maxotar/metro/electrical/datasheets/ATtiny1616 20 Pin VQFN.PNG

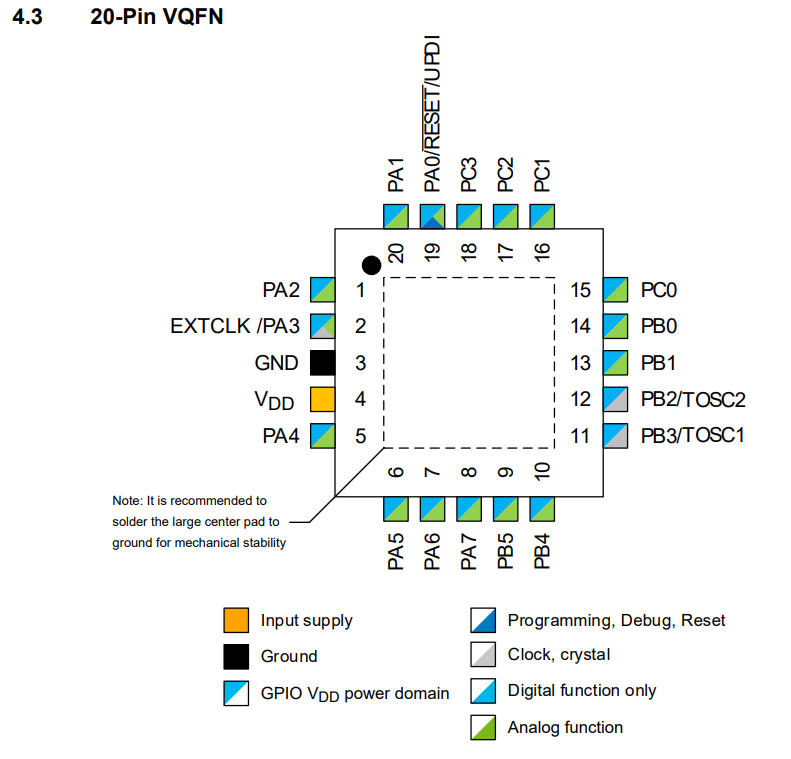
electrical/datasheets/ATtiny1616 20 Pin VQFN.PNG
