maxotar/metro/electrical/datasheets/ATtiny1616 MUX and PORTS.PNG

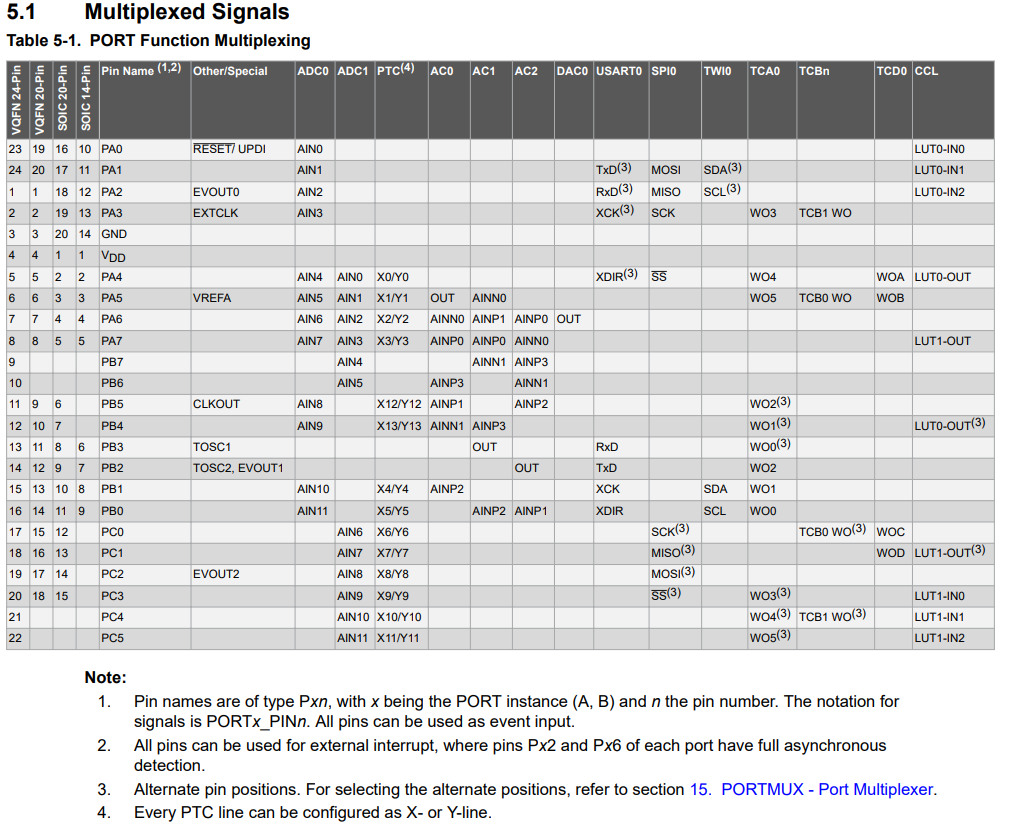
electrical/datasheets/ATtiny1616 MUX and PORTS.PNG
