maxotar/metro/electrical/references/Suggested Circuit DRV2605L.PNG

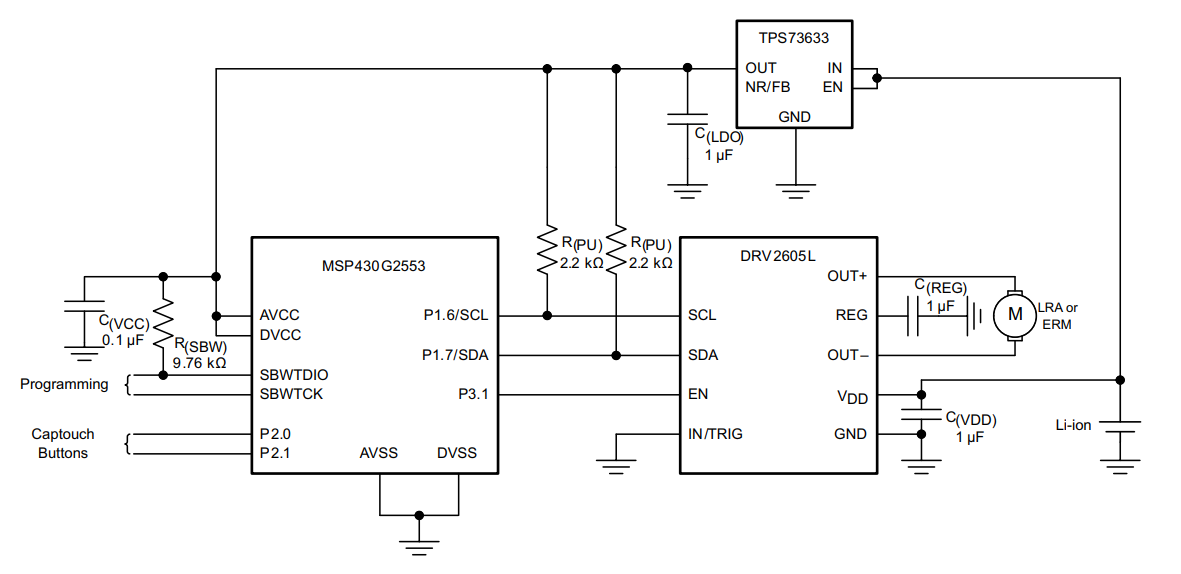
electrical/references/Suggested Circuit DRV2605L.PNG
