maxotar/metro/electrical/references/Suggested Layout DRV2605L.PNG

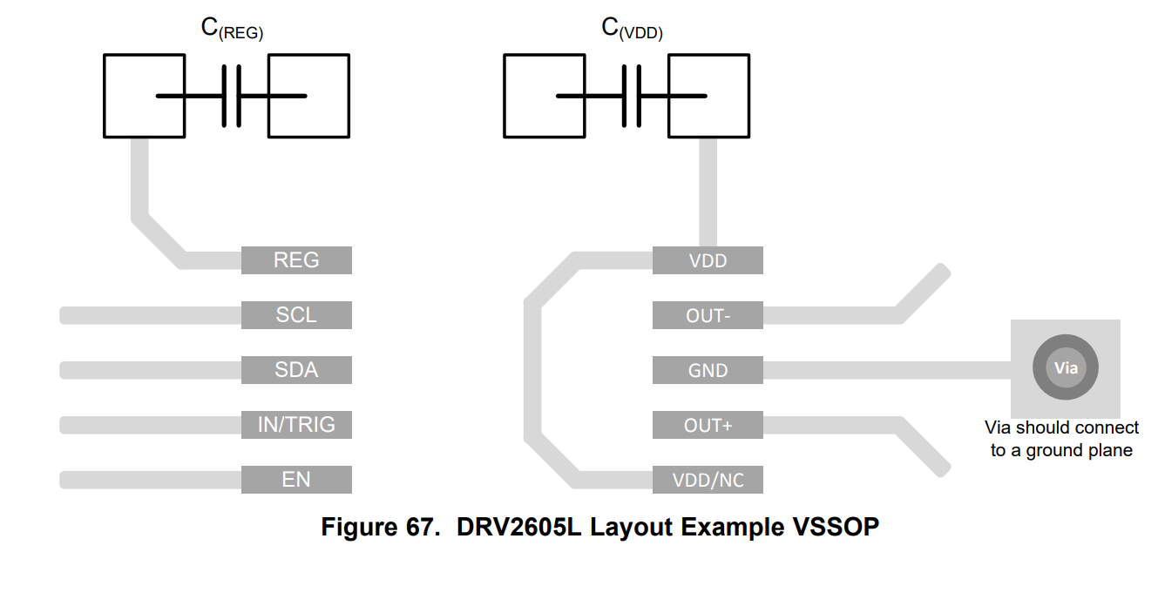
electrical/references/Suggested Layout DRV2605L.PNG
